second-state/vibebuddy/docs/hardware-reference/atk-box3/19.png

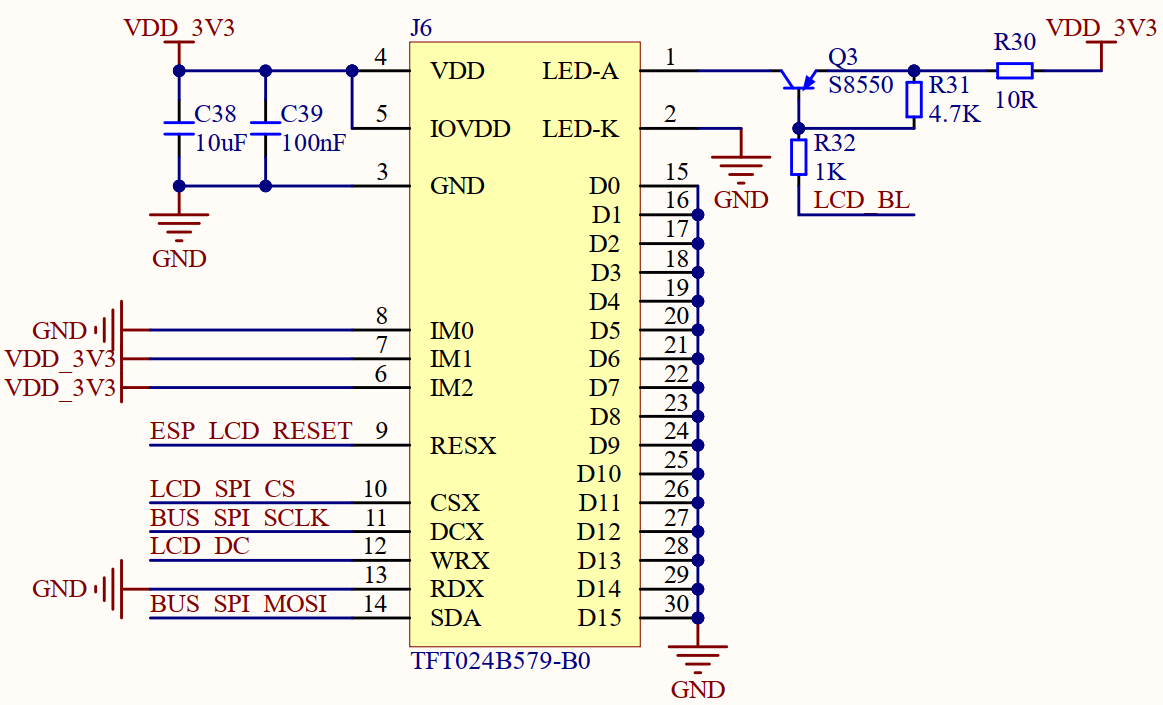
docs/hardware-reference/atk-box3/19.png
