second-state/vibebuddy/firmware/main/agent_display.h

#pragma once

#include <stdbool.h>
#include <stddef.h>

#include "esp_err.h"

#define AGENT_DISPLAY_MAX_TASKS 3
#define AGENT_DISPLAY_MAX_STATS 3

typedef enum {
  AGENT_DISPLAY_IDLE,
  AGENT_DISPLAY_WORKING,
  AGENT_DISPLAY_INPUT_REQUIRED,
  AGENT_DISPLAY_DONE,
  AGENT_DISPLAY_FAILED,
  AGENT_DISPLAY_OFFLINE,
} agent_display_state_t;

/// 小灯灵同一时刻只处于一个模式，每个模式拥有整块画面。值班盯着 Agent，
/// 番茄钟给用户计时，休闲是值班空闲够久之后自己去玩。Agent 状态在三个
/// 模式里都继续更新，只是番茄钟模式只给它留一行摘要。
typedef enum {
  AGENT_MODE_DUTY,
  AGENT_MODE_POMODORO,
  AGENT_MODE_LEISURE,
} agent_mode_t;

typedef struct {
  const char *title;
  agent_display_state_t state;
  /// 进入当前状态已经过去的秒数。设备收到后自行继续计时，因为可见状态
  /// 不变时 Mac 端不会再发消息，卡片上的数字却必须一直走。
  int elapsed_s;
  /// 所属项目；标题是会话名时画在第二行，空或与标题重复则不画。
  const char *project;
} agent_display_task_t;

esp_err_t agent_display_init(void);
esp_err_t agent_display_show(agent_display_state_t state, const char *title);
esp_err_t agent_display_show_tasks(agent_display_state_t state,
                                   const char *title,
                                   const agent_display_task_t *tasks,
                                   size_t task_count);
void agent_display_tick(void);

void agent_display_set_mode(agent_mode_t mode);
agent_mode_t agent_display_mode(void);
/// 立即重绘。按键改变了番茄钟之后不该再等下一帧动画。
void agent_display_refresh(void);
/// Agent 那边是否无事可做：主状态空闲且没有任务卡。休闲模式的无聊度
/// 按这个状态累计，而不是按多久没收到消息，因为长任务中途本来就没有消息。
bool agent_display_agent_idle(void);

/// 链路失联时覆盖显示：小灯灵闭眼，画面转灰。
/// 底层状态与任务卡保留，因为它们是最后已知的事实，只是不再可信。
void agent_display_set_link_lost(bool lost);

/// 眨眼确认：背光快闪约一秒，任何模式下都看得见。引导里用它认盒子。
void agent_display_identify(void);

/// 番茄钟阶段结束的闹铃：圆环先抖两秒，再整圈脉动，到用户按键或切走
/// 画面为止。静音时这是唯一的提醒。调用方随后要把番茄钟画面推到前面。
void agent_display_pomodoro_ended(void);

/// 静音时左上角常驻一个 MUTE 标记：静音是会被忘掉的状态，得一直看得见。
void agent_display_set_muted(bool muted);

/// 截图：把当前帧缓冲按行程编码逐行交给 `write_line`（不含换行）。
/// 第一行 `SHOT BEGIN 320x240 BACKLIGHT ON|OFF`，中间每行若干段
/// `rgb565:长度`，最后 `SHOT END`。
void agent_display_dump(void (*write_line)(const char *line));

/// 记录当日战绩，空闲屏会轮播这几行。下一次绘制时生效。
void agent_display_set_stats(const char *const *lines, size_t count);

/// 设置本机固件与 Mac 端的构建标识。设备会替用户比对两者：让人去读两串
/// 哈希再自己对比并不可靠，而不一致本身正是要看见的信号。
void agent_display_set_firmware_build(const char *build);
void agent_display_set_daemon_build(const char *build);
