second-state/vibebuddy/tools/device-screenshot.py

#!/usr/bin/env python3
"""从设备截图：发 `device.screenshot`，收行程编码的帧缓冲，写成 PNG。

要独占串口，先停掉 vibebuddyd（见 tools/screenshot.sh）。打开串口时不碰
DTR/RTS，设备不会复位，画面保持原样。
用法: device-screenshot.py PORT OUTPUT.png [scale]
"""

from __future__ import annotations

import struct
import sys
import time
import zlib

import serial

def rgb565_to_rgb(color: int) -> bytes:
    red = (color >> 11) & 0x1F
    green = (color >> 5) & 0x3F
    blue = color & 0x1F
    return bytes((red * 255 // 31, green * 255 // 63, blue * 255 // 31))


def write_png(path: str, pixels: list[bytes], scale: int, width: int, height: int) -> None:
    def chunk(kind: bytes, payload: bytes) -> bytes:
        body = kind + payload
        return struct.pack(">I", len(payload)) + body + struct.pack(">I", zlib.crc32(body) & 0xFFFFFFFF)

    raw = bytearray()
    for y in range(height):
        row = b"".join(pixels[y * width + x] * scale for x in range(width))
        for _ in range(scale):
            raw += b"\x00" + row
    header = struct.pack(">IIBBBBB", width * scale, height * scale, 8, 2, 0, 0, 0)
    with open(path, "wb") as output:
        output.write(b"\x89PNG\r\n\x1a\n")
        output.write(chunk(b"IHDR", header))
        output.write(chunk(b"IDAT", zlib.compress(bytes(raw), 6)))
        output.write(chunk(b"IEND", b""))


def main(argv: list[str]) -> int:
    if len(argv) not in (3, 4):
        print(__doc__, file=sys.stderr)
        return 2
    port_name, output_path = argv[1], argv[2]
    scale = int(argv[3]) if len(argv) == 4 else 2
    port = serial.Serial(port_name, 115200, timeout=0.5)
    port.reset_input_buffer()
    port.write(b'{"version":1,"event":"device.screenshot"}\n')

    pixels: list[bytes] = []
    backlight_on = True
    deadline = time.time() + 60
    started = False
    width, height = 0, 0
    while time.time() < deadline:
        line = port.readline().decode("utf-8", "replace").strip()
        if not line:
            continue
        if line.startswith("SHOT BEGIN"):
            width, height = map(int, line.split()[2].split("x"))
            if (width, height) not in ((320, 240), (240, 240)):
                raise ValueError("未知屏幕尺寸")
            pixels.clear()
            started = True
            backlight_on = "BACKLIGHT OFF" not in line
            continue
        if line == "SHOT END":
            break
        if not started or not line.startswith("SHOT "):
            continue
        for run in line[5:].split():
            color, count = run.split(":")
            pixels.extend([rgb565_to_rgb(int(color, 16))] * int(count))
    port.close()

    if not started or len(pixels) != width * height:
        print(f"帧不完整：收到 {len(pixels)} 像素，应为 {width * height}", file=sys.stderr)
        return 1
    if not backlight_on:
        # 背光关着，人眼看到的就是一块黑屏；把画面压暗到几乎不可见。
        pixels = [bytes(channel // 8 for channel in pixel) for pixel in pixels]
    write_png(output_path, pixels, scale, width, height)
    print(f"{output_path} 背光{'开' if backlight_on else '关'}")
    return 0


if __name__ == "__main__":
    sys.exit(main(sys.argv))
